Samuel-Lorza/Sistema-de-riego/Diagramas abstractos/Diagramas de flujo/Diagrama de flujo riego.jpg

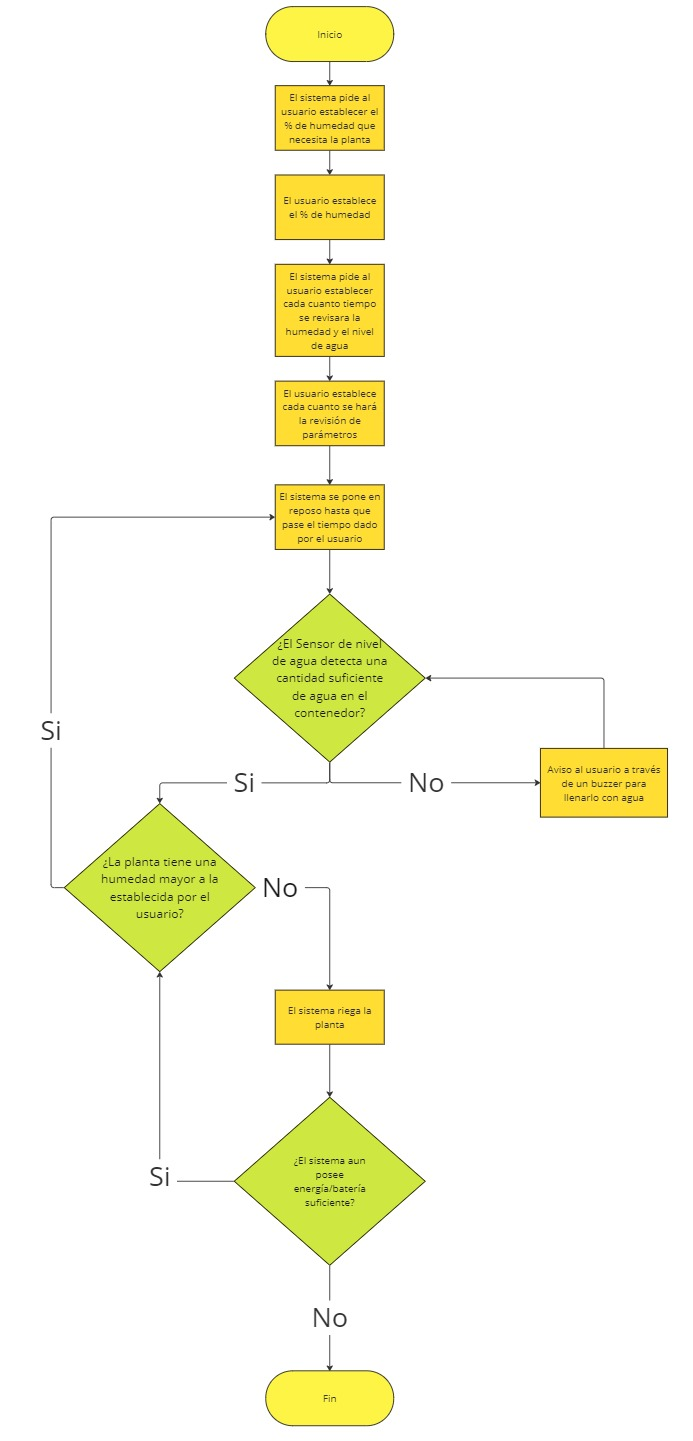
Diagramas abstractos/Diagramas de flujo/Diagrama de flujo riego.jpg
