Samuel-Lorza/Sistema-de-riego/Diagramas abstractos/Diagramas/Diagrama de Caja Negra.png

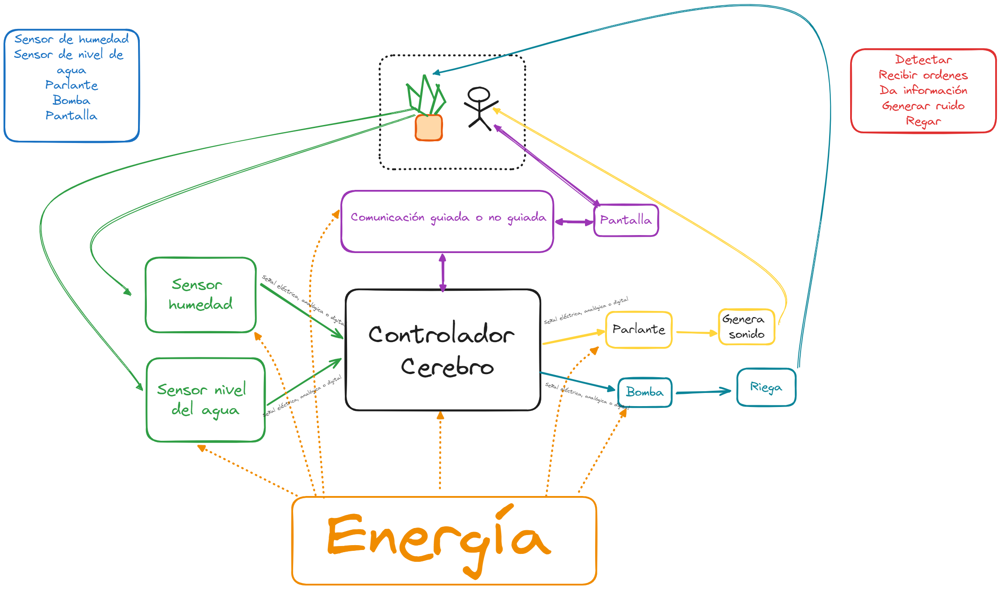
Diagramas abstractos/Diagramas/Diagrama de Caja Negra.png
