Samuel-Lorza/Sistema-de-riego/Diagramas abstractos/Diagramas/Diagrama tecnologico.png

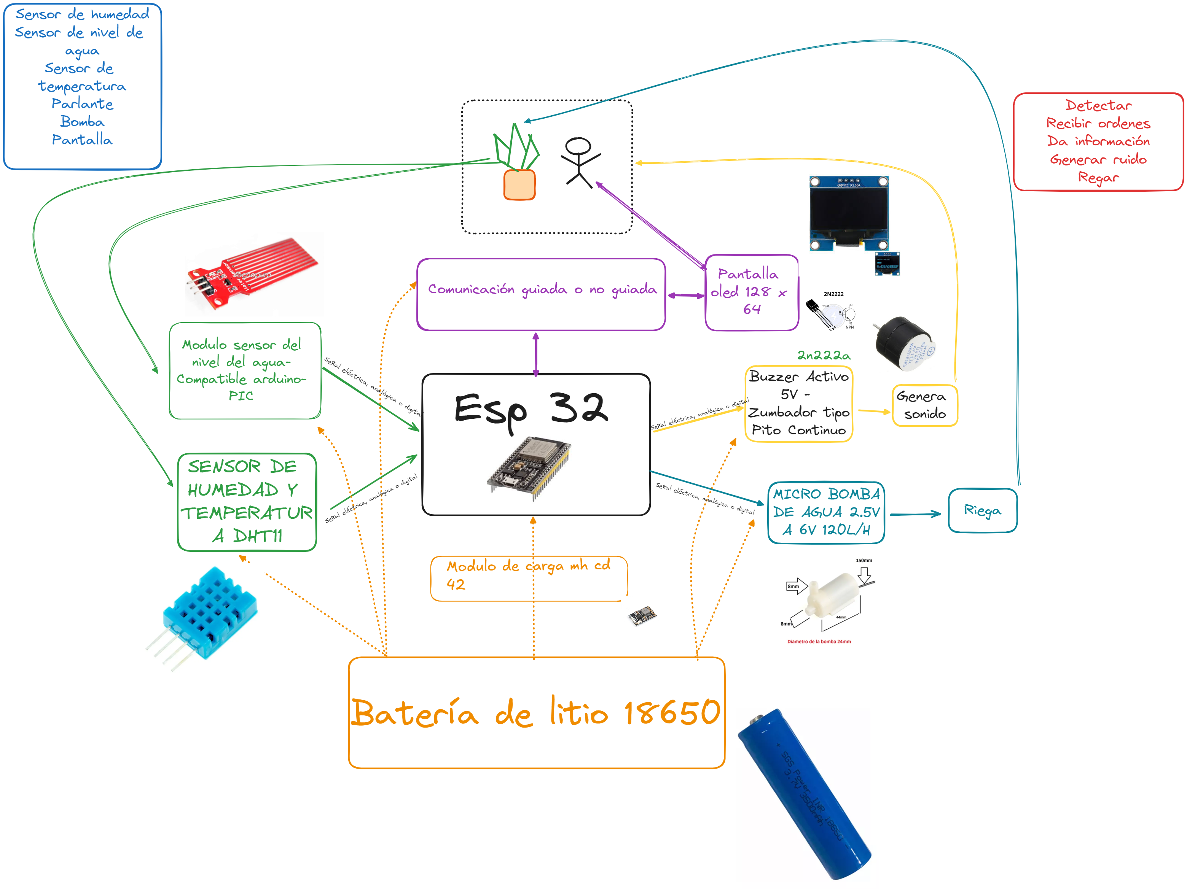
Diagramas abstractos/Diagramas/Diagrama tecnologico.png
