Samuel-Lorza/Sistema-de-riego/Imagenes Evidencia/Encuentro Ingenia Futuro 1.jpg

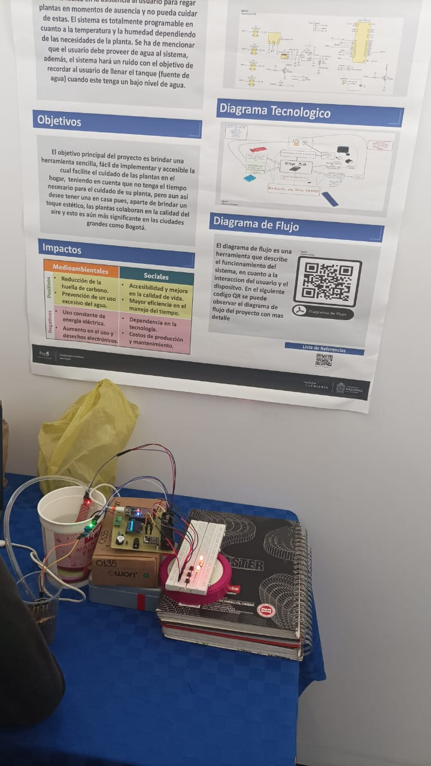
Imagenes Evidencia/Encuentro Ingenia Futuro 1.jpg
