Samuel-Lorza/Sistema-de-riego/Imagenes Evidencia/Encuentro Ingenia Futuro 2.jpg

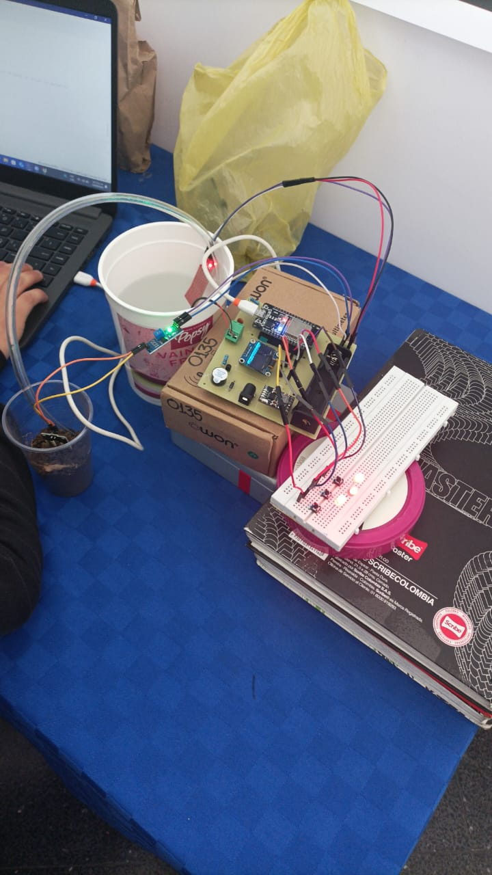
Imagenes Evidencia/Encuentro Ingenia Futuro 2.jpg
