Samuel-Lorza/Sistema-de-riego/Imagenes Evidencia/Encuentro Ingenia Futuro 3.jpg

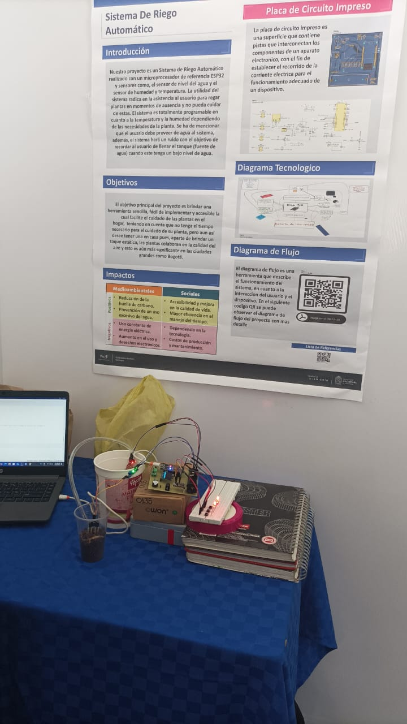
Imagenes Evidencia/Encuentro Ingenia Futuro 3.jpg
