Samuel-Lorza/Sistema-de-riego/Imagenes Evidencia/PCB con todos los elementos del proyecto.jpg

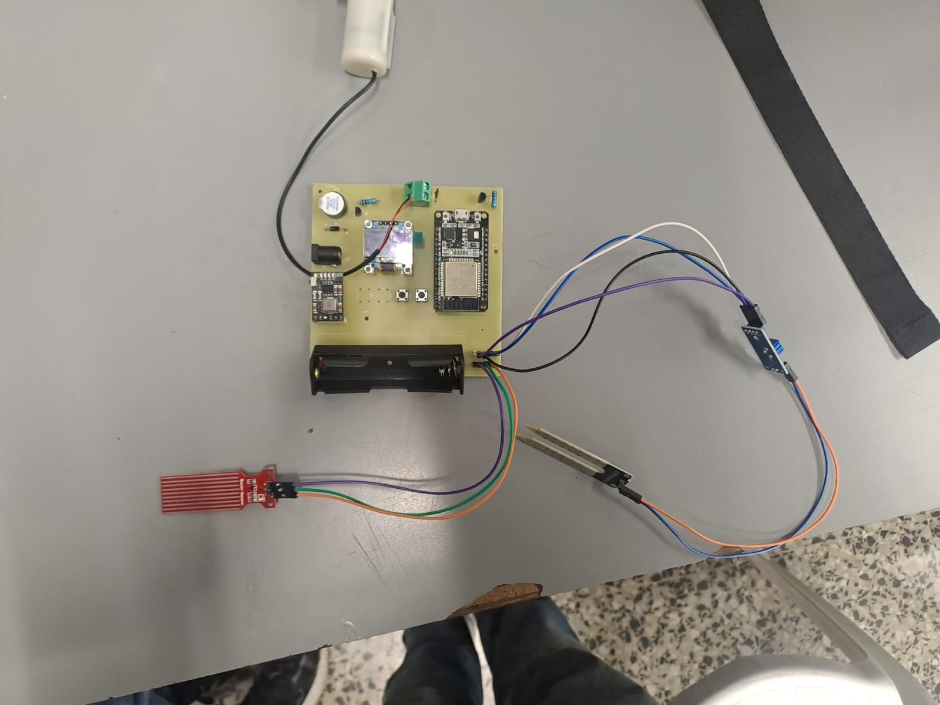
Imagenes Evidencia/PCB con todos los elementos del proyecto.jpg
