Samuel-Lorza/Sistema-de-riego/Imagenes Evidencia/PCB impresa con diagrama esquemático de fondo.jpg

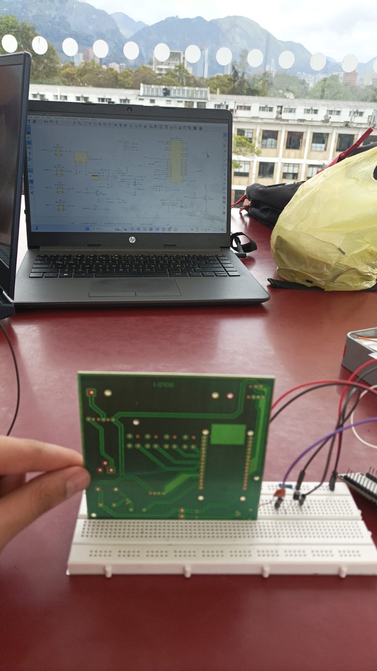
Imagenes Evidencia/PCB impresa con diagrama esquemático de fondo.jpg
