Samuel-Lorza/Sistema-de-riego/Imagenes Evidencia/PCB impresa vista frontal.jpg

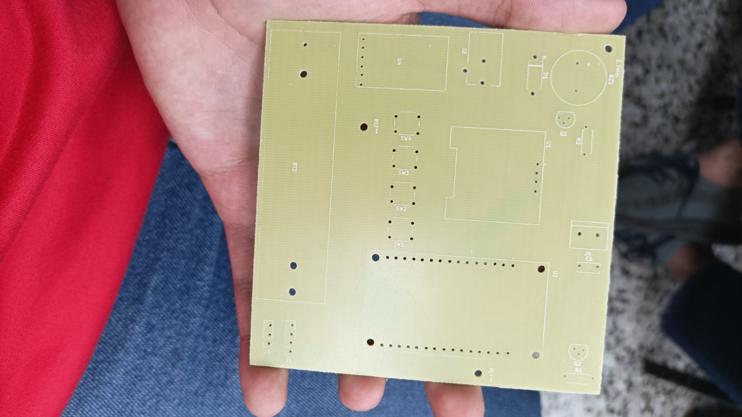
Imagenes Evidencia/PCB impresa vista frontal.jpg
