Samuel-Lorza/Sistema-de-riego/Diseño de PCB/PCB fabricada/PCB componentes soldados.jpg

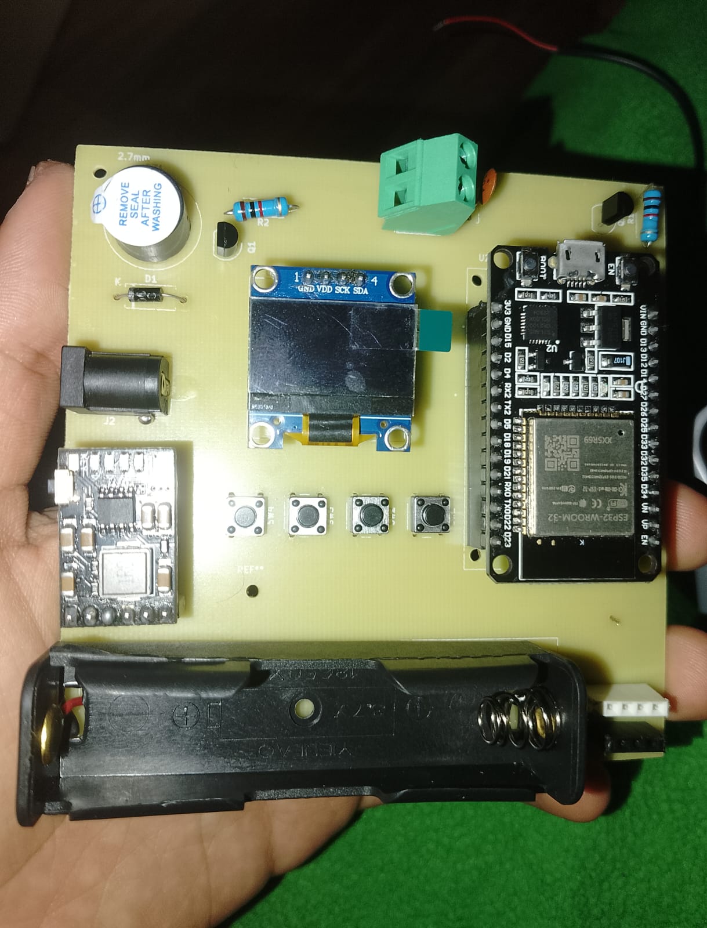
Diseño de PCB/PCB fabricada/PCB componentes soldados.jpg
