Samuel-Lorza/Sistema-de-riego/Imagenes Evidencia/PCB recién soldada con los pines y sus respectivos componentes vista frontal.jpg

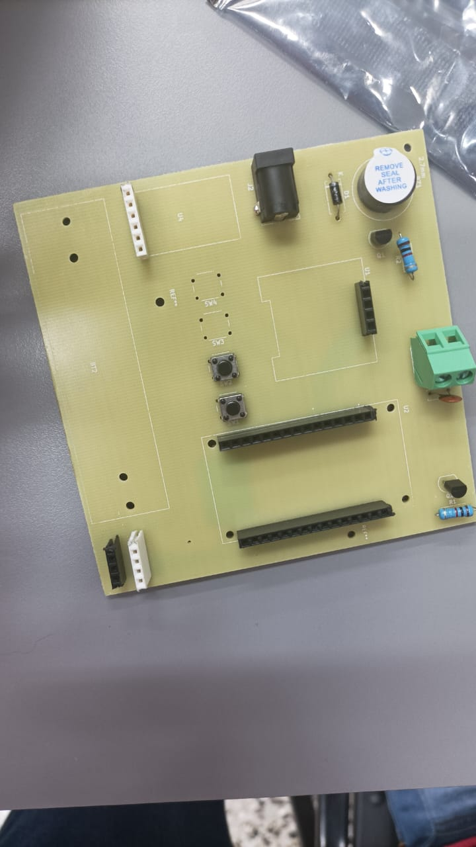
Imagenes Evidencia/PCB recién soldada con los pines y sus respectivos componentes vista frontal.jpg
