Samuel-Lorza/Sistema-de-riego/Imagenes Evidencia/PCB recién soldada con los pines y sus respectivos componentes vista posterior.jpg

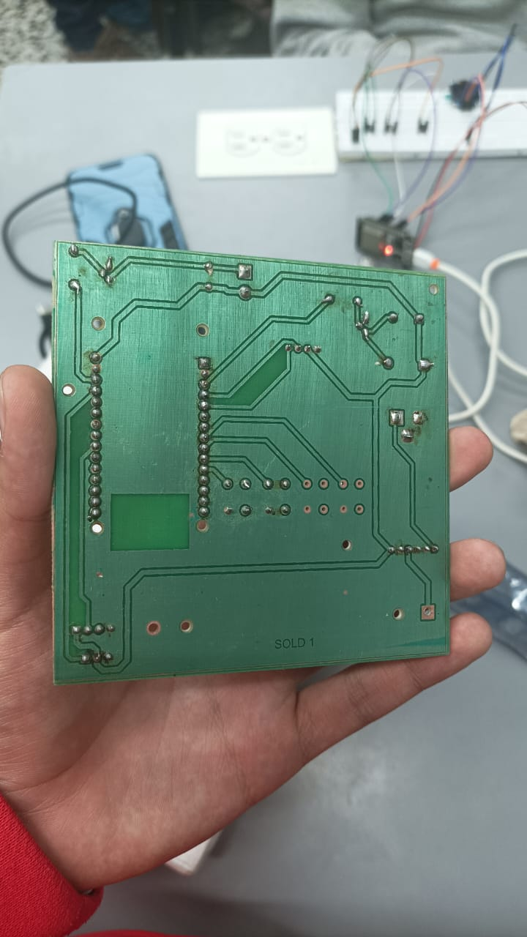
Imagenes Evidencia/PCB recién soldada con los pines y sus respectivos componentes vista posterior.jpg
