Samuel-Lorza/Sistema-de-riego/Diseño de PCB/PCB fabricada/PCB .jpg

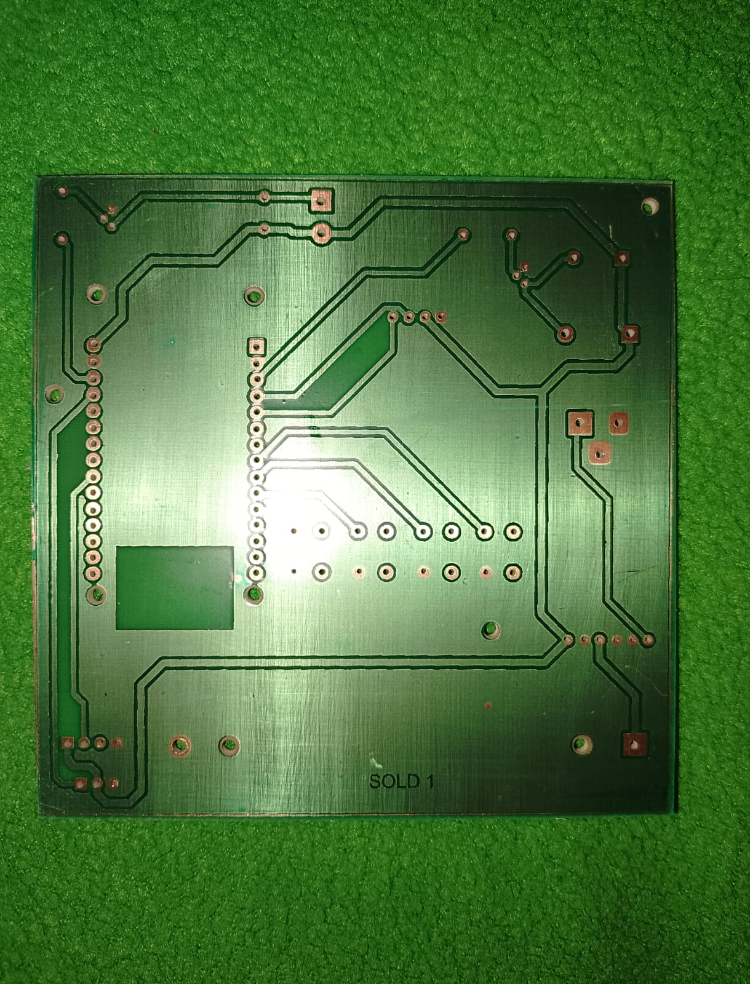
Diseño de PCB/PCB fabricada/PCB .jpg
