Samuel-Lorza/Sistema-de-riego/Diseño de PCB/PCB fabricada/PCB funcionando.jpg

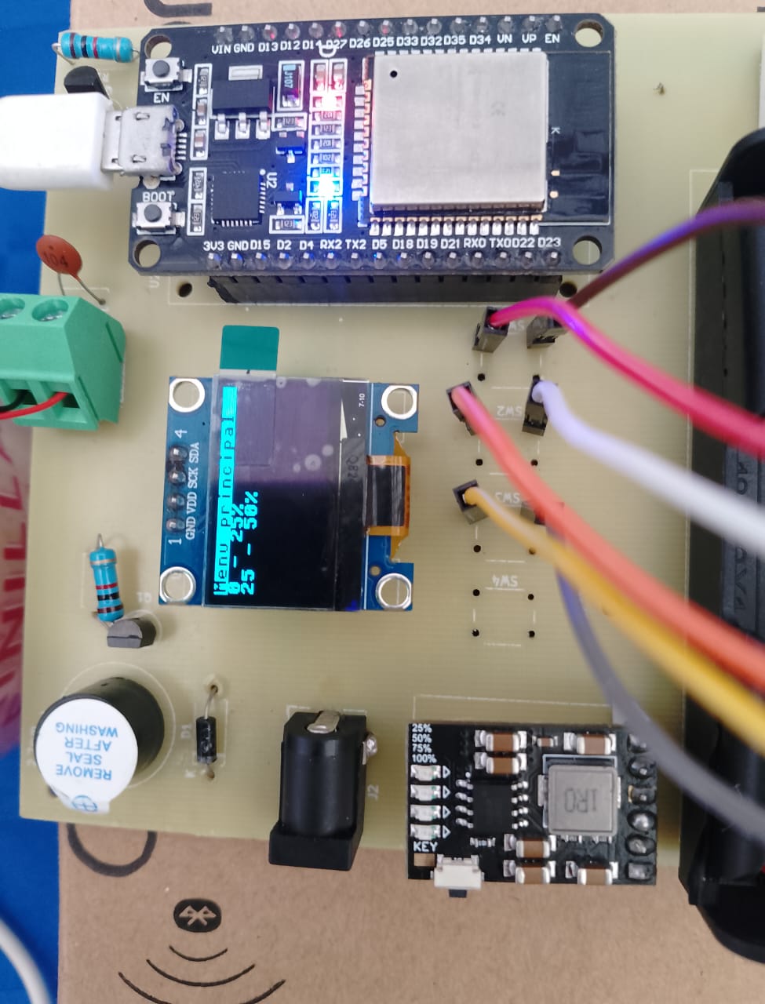
Diseño de PCB/PCB fabricada/PCB funcionando.jpg
