Samuel-Lorza/Sistema-de-riego/Diseño de PCB/PCB fabricada/PCB pines.jpg

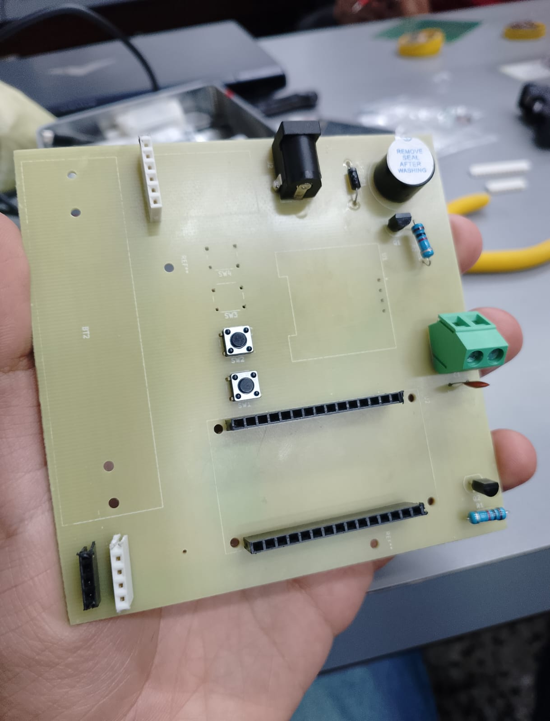
Diseño de PCB/PCB fabricada/PCB pines.jpg
