Samuel-Lorza/Sistema-de-riego/Diseño de PCB/PCB fabricada/PCB soldadura.jpg

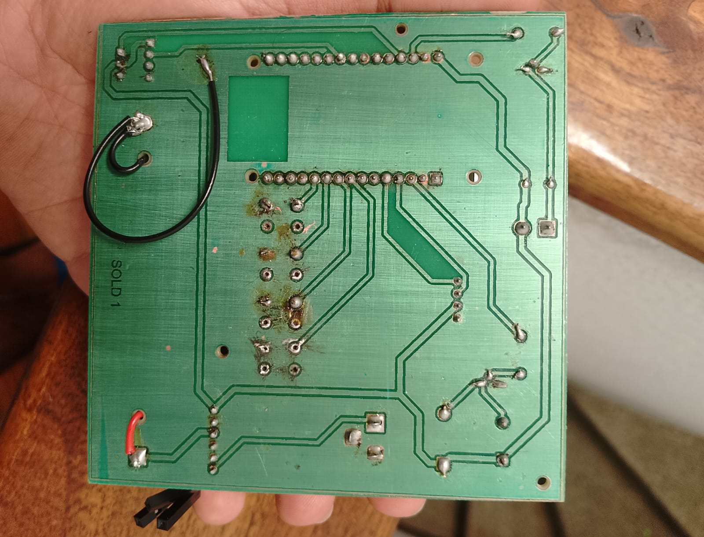
Diseño de PCB/PCB fabricada/PCB soldadura.jpg
