Samuel-Lorza/Sistema-de-riego/Imagenes Evidencia/Prueba de sensor de humedad y bomba de agua 2.jpg

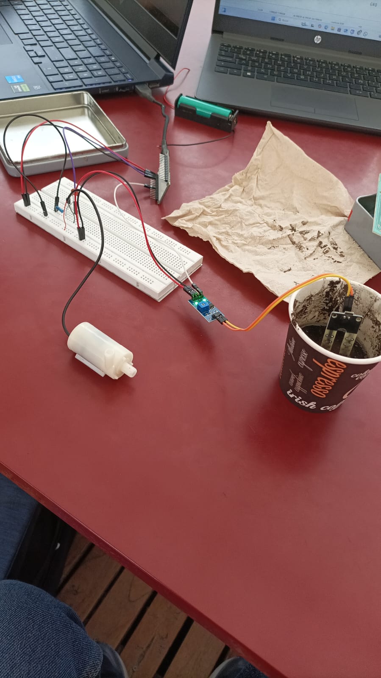
Imagenes Evidencia/Prueba de sensor de humedad y bomba de agua 2.jpg
