Samuel-Lorza/Sistema-de-riego/Imagenes Evidencia/Prueba de sensor de humedad y bomba de agua en protoboard.jpg

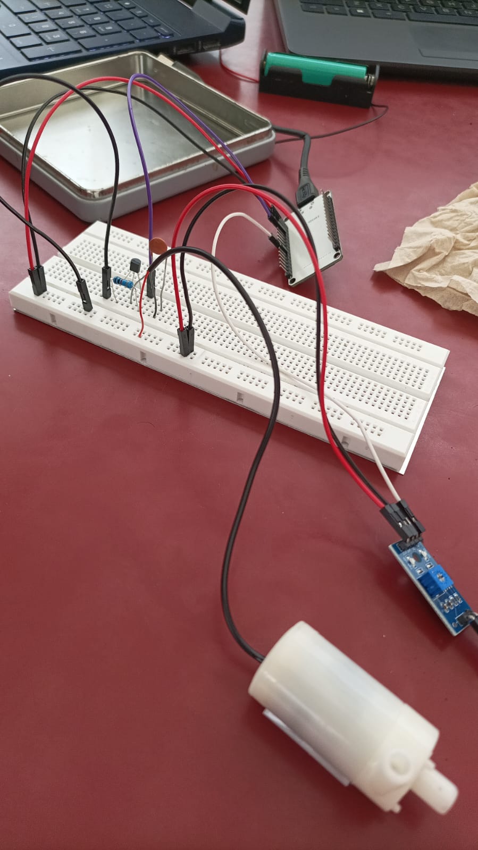
Imagenes Evidencia/Prueba de sensor de humedad y bomba de agua en protoboard.jpg
