Samuel-Lorza/Sistema-de-riego/Imagenes Evidencia/Prueba del sensor de nivel de agua en protoboard.jpg

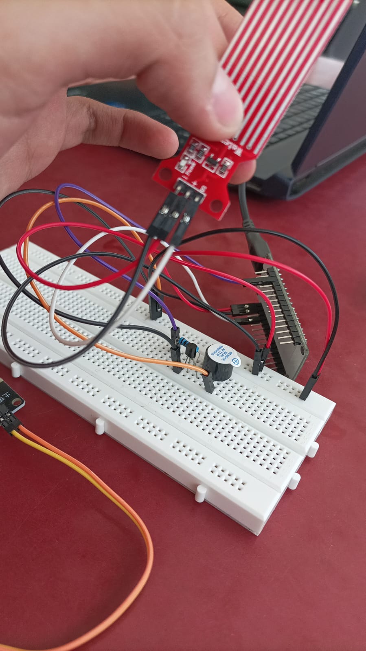
Imagenes Evidencia/Prueba del sensor de nivel de agua en protoboard.jpg
