Samuel-Lorza/Sistema-de-riego/Imagenes Evidencia/Soldadura de PCB , prueba de pantalla y medición de conductividad de la PCB.jpg

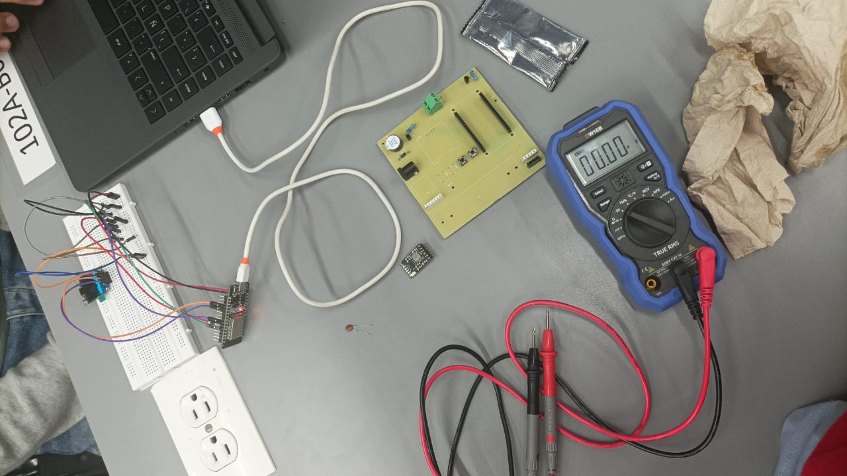
Imagenes Evidencia/Soldadura de PCB , prueba de pantalla y medición de conductividad de la PCB.jpg
